AlfonsoWD/ECEN404-2025SP-Pyro-Sensor/Presentations/PYRO SENSOR Status Update 5.pdf

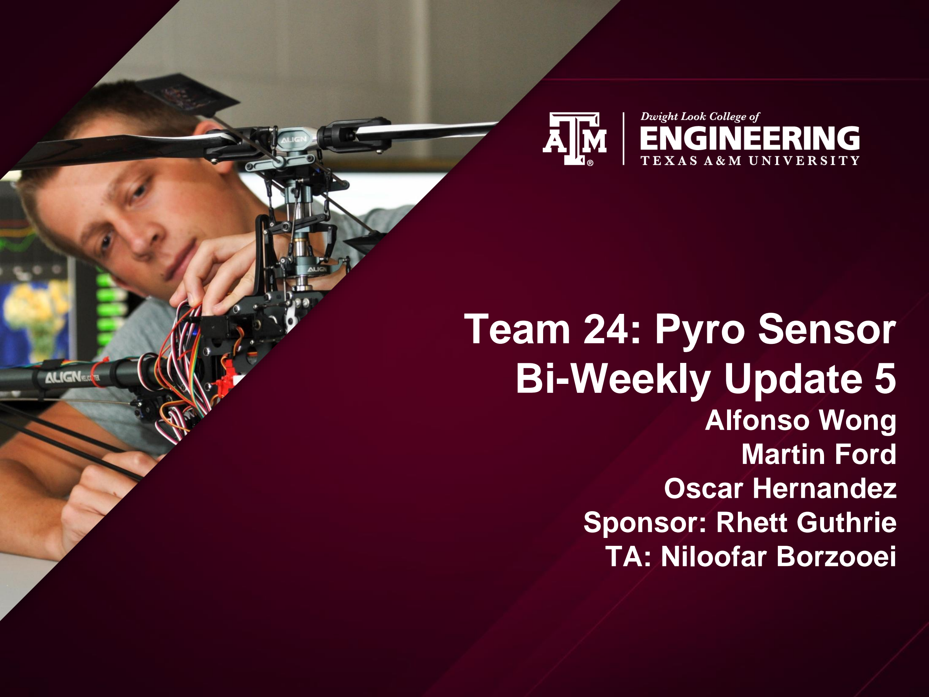
[picture p96: page 1]

# Team 24: Pyro Sensor Bi-Weekly Update 5

# Alfonso Wong Martin Ford Oscar Hernandez Sponsor: Rhett Guthrie TA: Niloofar Borzooei

# Project Summary

# - Problem statement:

# – Modern smoke detectors do not directly notify the emergency

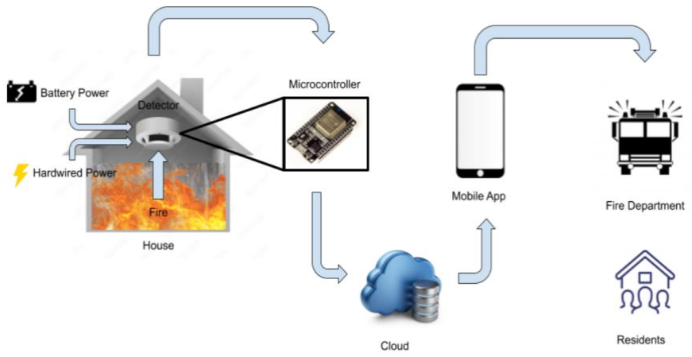
[picture p97: figure]

# responders – Fire department has limited data of residents in buildings

# - Our Pyro Sensor will:

# – Notify any user and emergency responders instantly through a mobile app of any incident – Give fire department information about residents and pets

# Integrated System Diagram

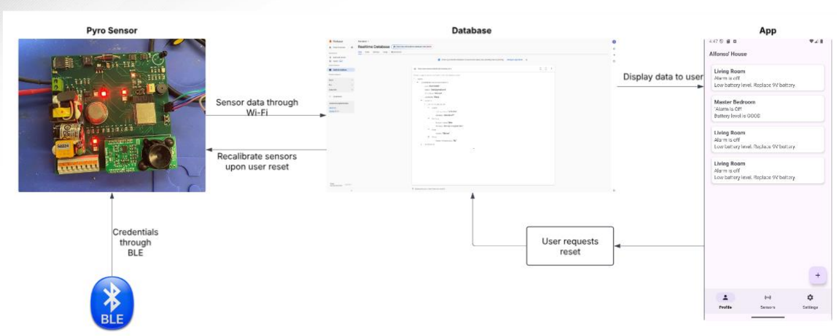
[picture p98: figure]

# Project Timeline

### Integration of mobile app and MCU (completed

2/28)

### Subsystem Designs and Testing (completed

3/1)

### Integration of Hardware and MCU (completed

3/2)

### Final Integration (completed

3/2)

### Full System Test (completed

3/22)

### Validation (to complete

by 4/3)

### Demo and Report (to complete

by 4/24)

# Martin Ford

Accomplishments since last update 15 hrs of effort | Ongoing progress/problems and plans until the next presentation
- Validated and tested full integrated system from signal reception to app notification | ● Ongoing validation for different scenarios ● Different levels/distances of IR, UV, smoke exposure

# Oscar Hernandez

# Accomplishments since last update 17 hrs of effort

# Ongoing progress/problems and plans until the next presentation

# - Validated correct system response to changes in the

inputs.

# - “Safe” notification in app

for normal conditions.

# - “Warning” for potential

hazard or low battery level.

# - “Alarm” notification for detected fire, and activate

device buzzer.

# - Tested that reset command from user shuts off buzzer (if active) and recalibrates

sensors.

# - Developing scenarios to verify system stability during Wi-Fi

loss and power outages.

# - On-going testing to verify that the device prevents going into Alarm mode from false alarm

sources.

# Alfonso Wong

# Accomplishments since last update 16 hrs of effort

# Ongoing progress/problems and plans until the next presentation

## - Validated correct system response

to changes in the inputs.

## - “Safe” notification in app for

normal conditions.

## - “Warning” for potential hazard

or low battery level.

## - “Alarm” notification for detected fire - Validated alert text notification to central dispatcher - Validated firefighter sign in and sensor view

## - Validated sensor connection to mobile app

# - Need to validate picture uploads - Fire time-tracker is having some errors. Need to fix and validate

# Mobile App Interface

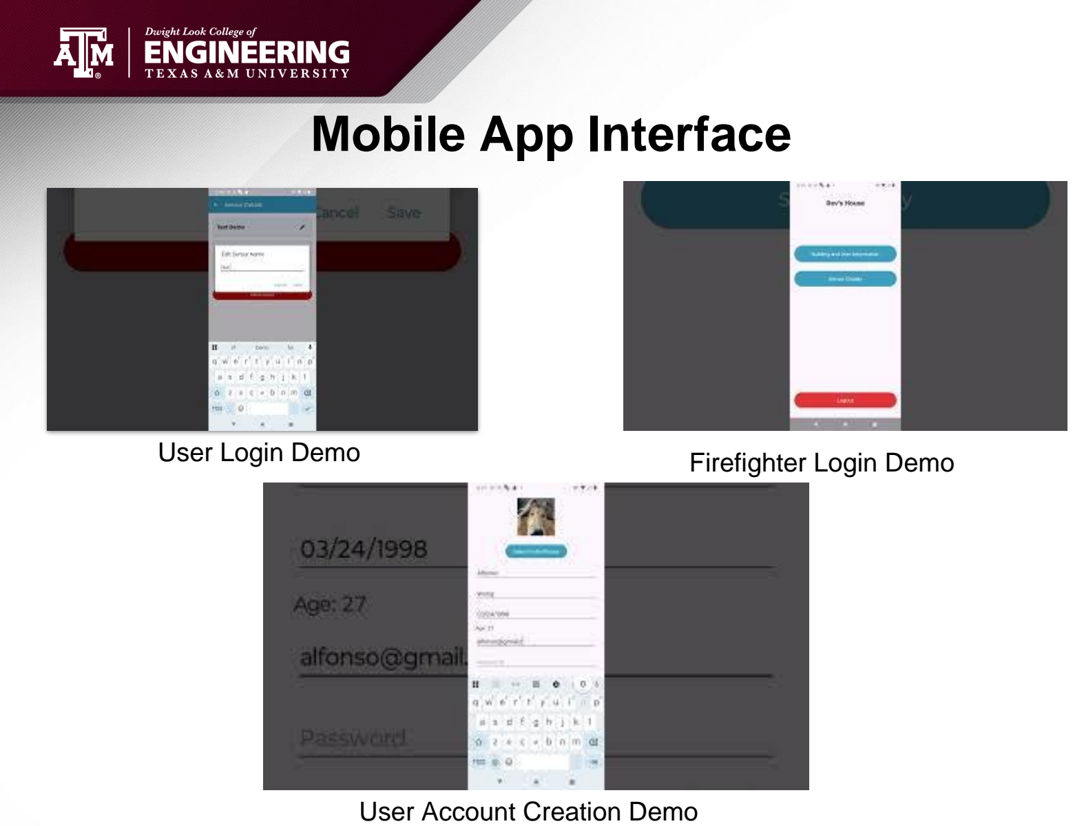
[picture p99: page 8]

Pyro Sensor Account Sign-in Demo (http://www.youtube.com/watch?v=e06_3-5AodU)

PYRO Sensor Firefighter Sign-in Demo (http://www.youtube.com/watch?v=mIK3reX92Vk)

PYRO SENSOR Account Creation Demo (http://www.youtube.com/watch?v=otN8RTRJRSw)

User Login Demo | Firefighter Login Demo

## User Account Creation Demo

# Device Initialization and Real-Time Fire Response

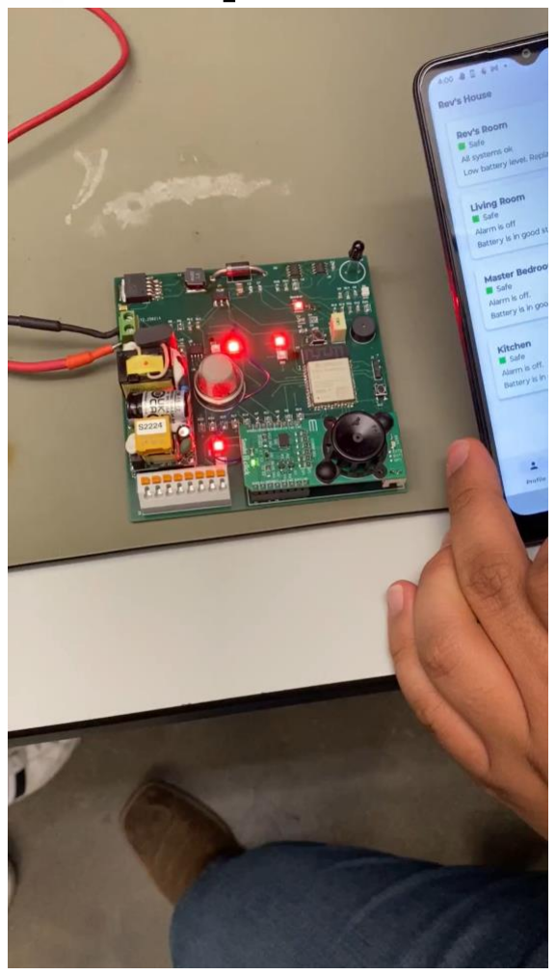
[picture p100: figure]

# Execution Plan

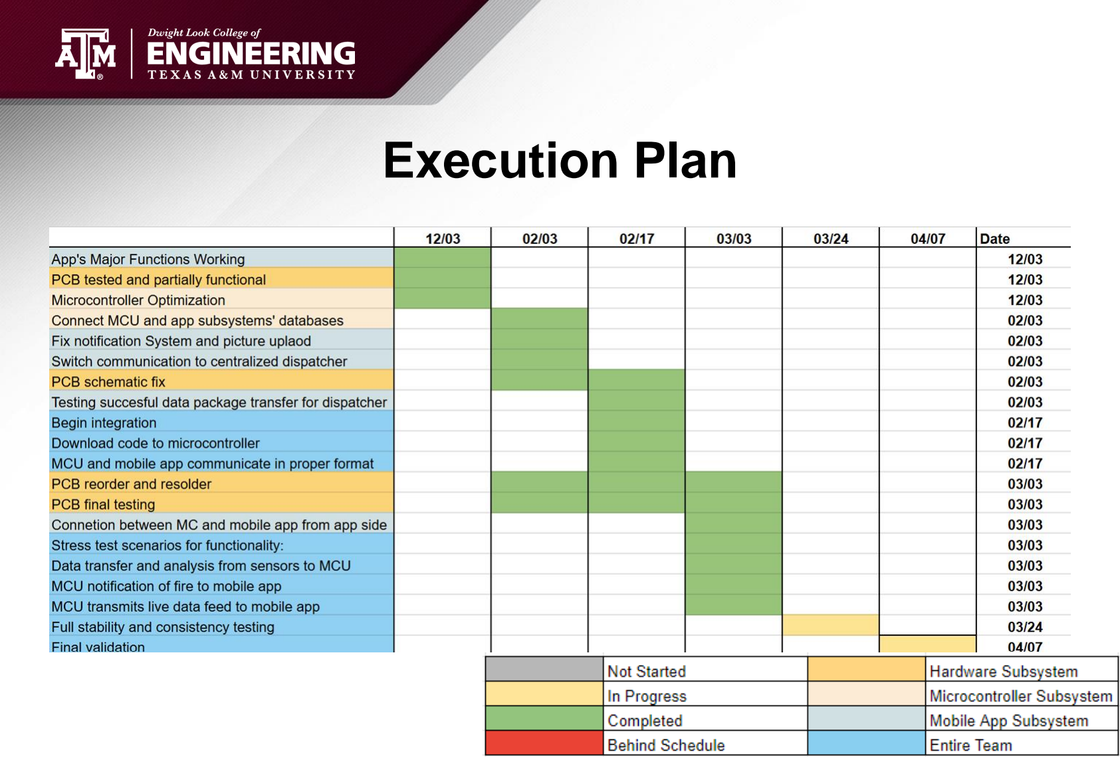
[picture p101: page 10]

# Validation Plan

Paragraph # | Test Name | Success Criteria | Status | Responsible Engineers
3.2.1.1 | Sensor Functionality | Sensors detect smoke/flame at expected ranges and output a signal. | Tested | Martin Ford
3.2.2.6 | Speaker Functionality | Speaker emits sound from signal at rated buzzer volume output. | Tested | Martin Ford
3.2.2.5 | Operating Time | System operates and receives full power continuously for 1 hour on each power source. | Untested | Martin Ford
3.2.1.4 | Network | MCU is able to aggregate data from sensors to a Access Point. | Tested | Oscar Hernandez
3.2.1.14 | Trouble Signal | MCU sends trouble signal to app for malfunctions. | Tested | Oscar Hernandez
3.2.1.8 | User Profile Creation | User is able to create an account and be able to sign in. | Tested | Alfonso Wong
3.2.1.9 | Push Notifications | Be able to push notifications to users and send text to central dispatcher. | Tested | Alfonso Wong
3.2.1.10 | Design UI | Have a working UI and test with emulator. | Tested | Alfonso Wong
3.2.1.11 | Integrate Cloud Service | Mobile app has ability to pull data from cloud service and display it. | Tested | Alfonso Wong

# Validation Plan

Paragraph # | Test Name | Success Criteria | Status | Responsible Engineers
3.2.1.6 | App compatible on Android devices | App can be used on most Android devices | Tested | Alfonso Wong
3.2.1.1 | MCU Peripherals Interface | MCU reads signals from all sensors, and activates/deactivates alarm. | Tested | Martin Ford & Oscar Hernandez
3.2.1.12 | Device and Application Communication | A new device can be added to user profile in application. | Tested | Alfonso Wong & Oscar Hernandez
3.2.2.13 | Real Time Communication | MCU is feeding constant information to database and it is being displayed in real time in mobile application. | Tested | Alfonso Wong & Oscar Hernandez
3.2.1.9 | Trigger Warning from MC | MCU must send a trigger alert of ongoing event and application must send notification to user and dispatch | Tested | Alfonso Wong & Oscar Hernandez
3.2.1.5 | Early Fire Detection | The system reduces the propagation of a fire by minimizing false alarms and notifying the user or fire department as soon as a fire is detected. | Untested | All

# Thank you for your attention!

# Questions?
