AlfonsoWD/ECEN404-2025SP-Pyro-Sensor/MCU Firmware/components/Smoke_Sensor/include/Smoke_Sensor.h

/* Define to prevent recursive inclusion -------------------------------------*/
#ifndef SMOKE_SENSOR
#define SMOKE_SENSOR

#ifdef __cplusplus
extern "C" {
#endif

/* Includes ------------------------------------------------------------------*/
#include <stdio.h>
#include <stdlib.h>
#include <stdint.h>
#include <stdbool.h>

#include "driver/i2c_master.h"
#include "driver/gpio.h"

/* Exported Macros -----------------------------------------------------------*/

typedef struct {
	char message[100];
	bool sensor_warning;
	bool sensor_confirmed;
	bool sensor_confirmed_extreme;
} SmokeSensorData;


/* ADPD188 I2C device address */
#define ADPD188BI_I2C_ADDR							0x64

/* ADPD188 registers */
#define ADPD188BI_REG_STATUS						0x00
#define ADPD188BI_REG_INT_MASK					0x01
#define ADPD188BI_REG_GPIO_DRV					0x02
#define ADPD188BI_REG_BG_STATUS					0x04
#define ADPD188BI_REG_FIFO_THR					0x06
#define ADPD188BI_REG_DEVID							0x08
#define ADPD188BI_REG_I2CS_ID						0x09
#define ADPD188BI_REG_CLK_RATIO					0x0A
#define ADPD188BI_REG_GPIO_CTRL					0x0B
#define ADPD188BI_REG_SLAVE_ADDR_KEY		0x0D
#define ADPD188BI_REG_SW_RESET					0x0F
#define ADPD188BI_REG_MODE							0x10
#define ADPD188BI_REG_SLOT_EN						0x11
#define ADPD188BI_REG_FSAMPLE						0x12
#define ADPD188BI_REG_PD_LED_SELECT			0x14
#define ADPD188BI_REG_NUM_AVG						0x15
#define ADPD188BI_REG_BIG_MEAS_A				0x16
#define ADPD188BI_REG_INT_SEQ_A					0x17
#define ADPD188BI_REG_SLOTA_CH1_OFFSET	0x18
#define ADPD188BI_REG_SLOTA_CH2_OFFSET	0x19
#define ADPD188BI_REG_SLOTA_CH3_OFFSET	0x1A
#define ADPD188BI_REG_SLOTA_CH4_OFFSET	0x1B
#define ADPD188BI_REG_BIG_MEAS_B				0x1C
#define ADPD188BI_REG_INT_SEQ_B					0x1D
#define ADPD188BI_REG_SLOTB_CH1_OFFSET	0x1E
#define ADPD188BI_REG_SLOTB_CH2_OFFSET	0x1F
#define ADPD188BI_REG_SLOTB_CH3_OFFSET	0x20
#define ADPD188BI_REG_SLOTB_CH4_OFFSET	0x21
#define ADPD188BI_REG_ILED3_COARSE			0x22
#define ADPD188BI_REG_ILED1_COARSE			0x23
#define ADPD188BI_REG_ILED2_COARSE			0x24
#define ADPD188BI_REG_ILED_FINE					0x25
#define ADPD188BI_REG_SLOTA_LED_PULSE		0x30
#define ADPD188BI_REG_SLOTA_NUM_PULSES	0x31
#define ADPD188BI_REG_LED_DISABLE				0x34
#define ADPD188BI_REG_SLOTB_LED_PULSE		0x35
#define ADPD188BI_REG_SLOTB_NUM_PULSES	0x36
#define ADPD188BI_REG_ALT_PWR_DN				0x37
#define ADPD188BI_REG_EXT_SYNC_STARTUP	0x38
#define ADPD188BI_REG_SLOTA_AFE_WINDOW	0x39
#define ADPD188BI_REG_SLOTB_AFE_WINDOW	0x3B
#define ADPD188BI_REG_AFE_PWR_CFG1			0x3C
#define ADPD188BI_REG_SLOTA_FLOAT_LED		0x3E
#define ADPD188BI_REG_SLOTB_FLOAT_LED		0x3F
#define ADPD188BI_REG_SLOTA_TIA_CFG			0x42
#define ADPD188BI_REG_SLOTA_AFE_CFG			0x43
#define ADPD188BI_REG_SLOTB_TIA_CFG			0x44
#define ADPD188BI_REG_SLOTB_AFE_CFG			0x45
#define ADPD188BI_REG_SAMPLE_CLK				0x4B
#define ADPD188BI_REG_CLK32M_ADJUST			0x4D
#define ADPD188BI_REG_EXT_SYNC_SEL			0x4F
#define ADPD188BI_REG_CLK32M_CAL_EN			0x50
#define ADPD188BI_REG_AFE_PWR_CFG2			0x54
#define ADPD188BI_REG_TIA_INDEP_GAIN		0x55
#define ADPD188BI_REG_MATH							0x58
#define ADPD188BI_REG_FLT_CONFIG_B			0x59
#define ADPD188BI_REG_FLT_LED_FIRE			0x5A
#define ADPD188BI_REG_FLT_CONFIG_A			0x5E
#define ADPD188BI_REG_DATA_ACCESS_CTL		0x5F
#define ADPD188BI_REG_FIFO_ACCESS				0x60
#define ADPD188BI_REG_SLOTA_CH1					0x64
#define ADPD188BI_REG_SLOTA_CH2					0x65
#define ADPD188BI_REG_SLOTA_CH3					0x66
#define ADPD188BI_REG_SLOTA_CH4					0x67
#define ADPD188BI_REG_SLOTB_CH1					0x68
#define ADPD188BI_REG_SLOTB_CH2					0x69
#define ADPD188BI_REG_SLOTB_CH3					0x6A
#define ADPD188BI_REG_SLOTB_CH4					0x6B
#define ADPD188BI_REG_A_CH1_LOW					0x70
#define ADPD188BI_REG_A_CH2_LOW					0x71
#define ADPD188BI_REG_A_CH3_LOW					0x72
#define ADPD188BI_REG_A_CH4_LOW					0x73
#define ADPD188BI_REG_A_CH1_HIGH				0x74
#define ADPD188BI_REG_A_CH2_HIGH				0x75
#define ADPD188BI_REG_A_CH3_HIGH				0x76
#define ADPD188BI_REG_A_CH4_HIGH				0x77
#define ADPD188BI_REG_B_CH1_LOW					0x78
#define ADPD188BI_REG_B_CH2_LOW					0x79
#define ADPD188BI_REG_B_CH3_LOW					0x7A
#define ADPD188BI_REG_B_CH4_LOW					0x7B
#define ADPD188BI_REG_B_CH1_HIGH				0x7C
#define ADPD188BI_REG_B_CH2_HIGH				0x7D
#define ADPD188BI_REG_B_CH3_HIGH				0x7E
#define ADPD188BI_REG_B_CH4_HIGH				0x7F

/*  */
#define ADPD188BI_READ_CMD							0
#define ADPD188BI_WRITE_CMD							1



void smoke_task(void* param);

/* Exported typedef ----------------------------------------------------------*/
/**
 * @brief Smoke 2 description setting.
 */
typedef enum {
	ADPD188BI_SLOT_A = 0,
	ADPD188BI_SLOT_B = 4
} adpd188bi_slot_e;

/**
 * @brief Smoke 2 description setting to select channel.
 */
typedef enum {
	ADPD188BI_CH_1 = 0,
	ADPD188BI_CH_2,
	ADPD188BI_CH_3,
	ADPD188BI_CH_4
} adpd188bi_channel_e;

/**
 * @brief Smoke 2 description setting to select mode.
 */
typedef enum {
	ADPD188BI_MODE_IDLE = 0,
	ADPD188BI_MODE_PROGRAM,
	ADPD188BI_MODE_NORMAL
} adpd188bi_mode_e;

/**
 * @brief Smoke 2 description setting to select mode.
 */
typedef enum {
	ADPD188BI_SMOKE_ERROR = 0x0,
	ADPD188BI_SMOKE_DETECTED = 0xCC,
	ADPD188BI_SMOKE_NOT_DETECTED = 0xDD
} adpd188bi_smoke_e;

typedef struct {
	i2c_master_dev_handle_t i2c_dev;	/*!< I2C device handle */
	int int_gpio;
	uint16_t calib_value;
	uint16_t threshold_value;
	uint16_t enabled_slot;
} adpd188bi_t;


/* Exported variables --------------------------------------------------------*/

/* Exported functions prototypes ---------------------------------------------*/
/**
 * @brief Function to initialize a ADPD188 instance
 *
 * @param me             : Pointer to a adpd188bi_t instance
 * @param i2c_bus_handle : Handle to the I2C bus to add this device
 * @param dev_addr       : I2C device address
 *
 * @return ESP_OK on success
 */
esp_err_t adpd188bi_init(adpd188bi_t *const me, i2c_master_bus_handle_t i2c_bus_handle,
	uint8_t dev_addr, int int_gpio, bool Reset);

/**
 * @brief Function to set the working mode of the ADPD188
 *
 * @param me   : Pointer to a adpd188bi_t instance
 * @param mode : Working mode: IDLE, PROGRAM and NORMAL.
 *
 * @return ESP_OK on success
 */
esp_err_t adpd188bi_set_mode(adpd188bi_t *const me, adpd188bi_mode_e mode);

/**
 * @brief Function to set the working mode of the ADPD188
 *
 * @param me   : Pointer to a adpd188bi_t instance
 * @param mode : Working mode: IDLE, PROGRAM and NORMAL.
 *
 * @return ESP_OK on success
 */
esp_err_t adpd188bi_get_mode(adpd188bi_t *const me, adpd188bi_mode_e *mode);

/**
 * @brief Function to perform a software reset
 *
 * @param me : Pointer to a adpd188bi_t instance
 *
 * @return ESP_OK on success
 */
esp_err_t adpd188bi_soft_reset(adpd188bi_t *const me);

/**
 * @brief Function to perform a software reset todo: write correctly
 *
 * @param me : Pointer to a adpd188bi_t instance
 *
 * @return ESP_OK on success
 */
esp_err_t adpd188bi_get_int(adpd188bi_t *const me, uint8_t *fifo, uint8_t *slot_a,
		uint8_t *slot_b);

/**
 * @brief Function to perform a software reset todo: write correctly
 *
 * @param me : Pointer to a adpd188bi_t instance
 *
 * @return ESP_OK on success
 */
esp_err_t adpd188bi_read_sens_data(adpd188bi_t *const me, uint8_t slot, uint8_t ch,
		uint16_t *data);

/**
 * @brief Function to perform a software reset todo: write correctly
 *
 * @param me : Pointer to a adpd188bi_t instance
 *
 * @return ESP_OK on success
 */
esp_err_t adpd188bi_set_bit(adpd188bi_t *const me, uint8_t reg_addr, uint8_t bit_num,
		bool bit_val);

/**
 * @brief Function to perform a software reset todo: write correctly
 *
 * @param me : Pointer to a adpd188bi_t instance
 *
 * @return ESP_OK on success
 */
esp_err_t adpd188bi_set_bit_mask(adpd188bi_t *const me, uint8_t reg_addr,
		uint8_t bits_num,	uint16_t bits_val);

/**
 * @brief Function to perform a software reset todo: write correctly
 *
 * @param me : Pointer to a adpd188bi_t instance
 *
 * @return ESP_OK on success
 */
esp_err_t adpd188bi_calibration(adpd188bi_t *const me, uint16_t threshold);

/**
 * @brief Function to perform a software reset todo: write correctly
 *
 * @param me : Pointer to a adpd188bi_t instance
 *
 * @return ESP_OK on success
 */
uint16_t adpd188bi_get_calib(adpd188bi_t *const me);

/**
 * @brief Function to perform a software reset todo: write correctly
 *
 * @param me : Pointer to a adpd188bi_t instance
 *
 * @return ESP_OK on success
 */
esp_err_t adpd188bi_check_smoke(adpd188bi_t *const me, adpd188bi_smoke_e *smoke);

/**
 * @brief Function to perform a software reset todo: write correctly
 *
 * @param me : Pointer to a adpd188bi_t instance
 *
 * @return ESP_OK on success
 */
int adpd188bi_get_int_gpio(adpd188bi_t *const me);


void smoke_task(void* param);
float get_BLUE_OVER_IR_ratio_standby(adpd188bi_t *const device);
float get_BLUE_OVER_IR_ratio_clean(adpd188bi_t *const device);


#ifdef __cplusplus
}
#endif

#endif /* SMOKE_SENSOR */

/***************************** END OF FILE ************************************/
