AlfonsoWD/ECEN404-2025SP-Pyro-Sensor/MCU Firmware/components/Speaker/include/Speaker.h

#ifndef SPEAKER_H
#define SPEAKER_H

#ifdef __cplusplus
extern "C" {
#endif

void setup_pwm();
void start_alarm();
void stop_alarm();
void trigger_alarm();
void disable_alarm();
void soundSpeaker(void *param);

#ifdef __cplusplus
}
#endif

#endif // SPEAKER_H
